sora-jp/A2B-Ambisonic-Microphone/firmware_iface/src/a2b_regs.h

#ifndef A2B_REGS_H_
#define A2B_REGS_H_

#define A2B_CHIP 0x00
#define A2B_NODEADR 0x01
#define A2B_VENDOR 0x02
#define A2B_PRODUCT 0x03
#define A2B_VERSION 0x04
#define A2B_CAPABILITY 0x05
#define A2B_SWCTL 0x09
#define A2B_BCDNSLOTS 0x0A
#define A2B_LDNSLOTS 0x0B
#define A2B_LUPSLOTS 0x0C
#define A2B_DNSLOTS 0x0D
#define A2B_UPSLOTS 0x0E
#define A2B_RESPCYCS 0x0F
#define A2B_SLOTFMT 0x10
#define A2B_DATCTL 0x11
#define A2B_CONTROL 0x12
#define A2B_DISCVRY 0x13
#define A2B_SWSTAT 0x14
#define A2B_INTSTAT 0x15
#define A2B_INTSRC 0x16
#define A2B_INTTYPE 0x17
#define A2B_INTPND0 0x18
#define A2B_INTPND1 0x19
#define A2B_INTPND2 0x1A
#define A2B_INTMSK0 0x1B
#define A2B_INTMSK1 0x1C
#define A2B_INTMSK2 0x1D
#define A2B_BECCTL 0x1E
#define A2B_BECNT 0x1F
#define A2B_TESTMODE 0x20
#define A2B_ERRCNT0 0x21
#define A2B_ERRCNT1 0x22
#define A2B_ERRCNT2 0x23
#define A2B_ERRCNT3 0x24
#define A2B_NODE 0x29
#define A2B_DISCSTAT 0x2B
#define A2B_TXACTL 0x2E
#define A2B_TXBCTL 0x30
#define A2B_LINTTYPE 0x3E
#define A2B_I2CCFG 0x3F
#define A2B_PLLCTL 0x40
#define A2B_I2SGCFG 0x41
#define A2B_I2SCFG 0x42
#define A2B_I2SRATE 0x43
#define A2B_I2STXOFFSET 0x44
#define A2B_I2SRXOFFSET 0x45
#define A2B_SYNCOFFSET 0x46
#define A2B_PDMCTL 0x47
#define A2B_ERRMGMT 0x48
#define A2B_GPIODAT 0x4A
#define A2B_GPIODATSET 0x4B
#define A2B_GPIODATCLR 0x4C
#define A2B_GPIOOEN 0x4D
#define A2B_GPIOIEN 0x4E
#define A2B_GPIOIN 0x4F
#define A2B_PINTEN 0x50
#define A2B_PINTINV 0x51
#define A2B_PINCFG 0x52
#define A2B_I2STEST 0x53
#define A2B_RAISE 0x54
#define A2B_GENERR 0x55
#define A2B_I2SRRATE 0x56
#define A2B_I2SRRCTL 0x57
#define A2B_I2SRRSOFFS 0x58
#define A2B_CLK1CFG 0x59
#define A2B_CLK2CFG 0x5A
#define A2B_BMMCFG 0x5B
#define A2B_SUSCFG 0x5C
#define A2B_PDMCTL2 0x5D
#define A2B_UPMASK0 0x60
#define A2B_UPMASK1 0x61
#define A2B_UPMASK2 0x62
#define A2B_UPMASK3 0x63
#define A2B_UPOFFSET 0x64
#define A2B_DNMASK0 0x65
#define A2B_DNMASK1 0x66
#define A2B_DNMASK2 0x67
#define A2B_DNMASK3 0x68
#define A2B_DNOFFSET 0x69
#define A2B_CHIPID0 0x6A
#define A2B_CHIPID1 0x6B
#define A2B_CHIPID2 0x6C
#define A2B_CHIPID3 0x6D
#define A2B_CHIPID4 0x6E
#define A2B_CHIPID5 0x6F
#define A2B_GPIODEN 0x80
#define A2B_GPIOD0MSK 0x81
#define A2B_GPIOD1MSK 0x82
#define A2B_GPIOD2MSK 0x83
#define A2B_GPIOD3MSK 0x84
#define A2B_GPIOD4MSK 0x85
#define A2B_GPIOD5MSK 0x86
#define A2B_GPIOD6MSK 0x87
#define A2B_GPIOD7MSK 0x88
#define A2B_GPIODDAT 0x89
#define A2B_GPIODINV 0x8A
#define A2B_MBOX0CTL 0x90
#define A2B_MBOX0STAT 0x91
#define A2B_MBOX0B0 0x92
#define A2B_MBOX0B1 0x93
#define A2B_MBOX0B2 0x94
#define A2B_MBOX0B3 0x95
#define A2B_MBOX1CTL 0x96
#define A2B_MBOX1STAT 0x97
#define A2B_MBOX1B0 0x98
#define A2B_MBOX1B1 0x99
#define A2B_MBOX1B2 0x9A
#define A2B_MBOX1B3 0x9B

#endif // A2B_REGS_H_
